hermawandiki/Differential-Drive-Mobile-Robot/Hardware/Board.png

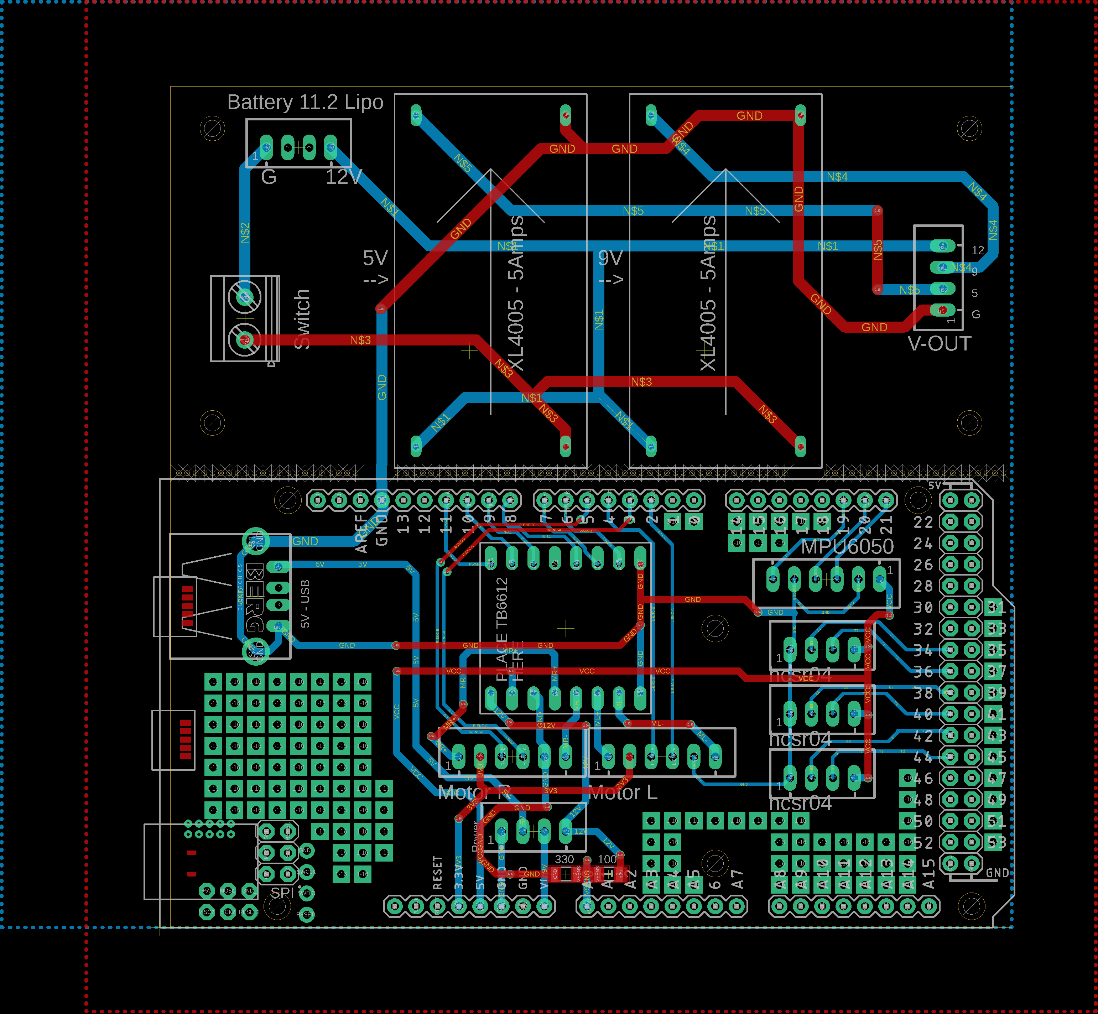
Hardware/Board.png
