hermawandiki/Differential-Drive-Mobile-Robot/Hardware/Skematik.png

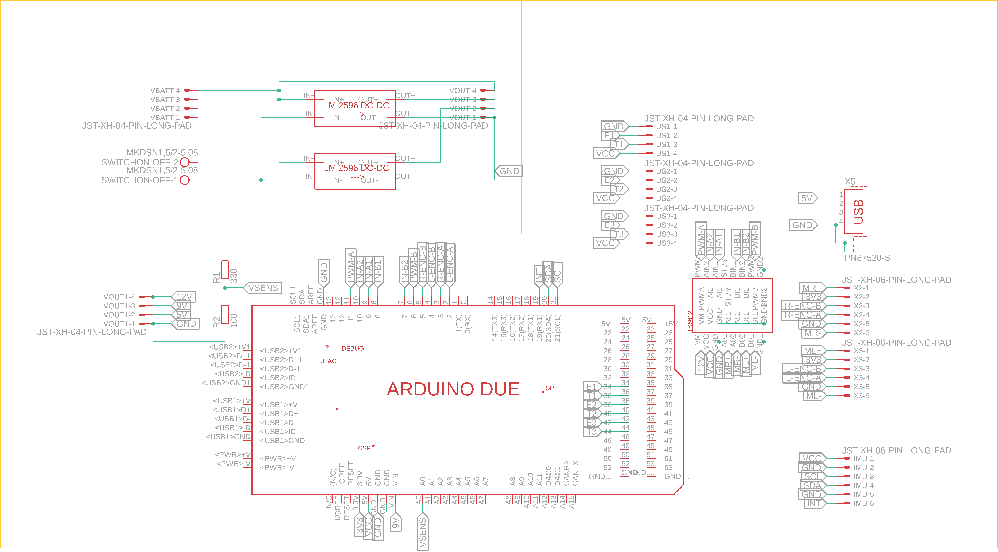
Hardware/Skematik.png
