hermawandiki/Differential-Drive-Mobile-Robot/GUI/build/assets/frame0/image_2.png

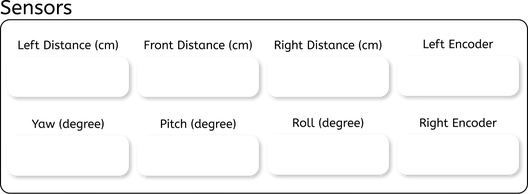
GUI/build/assets/frame0/image_2.png
